andyblarblar/timebay/rust_ws/sensor_node/src/dist_sensor.rs

//! Abstractions over the distance sensor

use async_trait::async_trait;
use rand::RngCore;
use std::cmp::max;
use std::io;
use std::time::Duration;
use tf_luna::TfLuna;
use thiserror::Error;

/// A sensor capable of reading distance values.
#[async_trait]
pub trait DistanceSensor {
    /// Gets a distance reading.
    async fn get_reading(&mut self) -> Result<DistanceReading, SensorError>;
}

/// Errors from interacting with the sensor
#[derive(Error, Debug)]
pub enum SensorError {
    #[error(transparent)]
    IOError(#[from] io::Error),
    #[error(transparent)]
    LunaErr(#[from] tf_luna::error::Error),
}

/// A distance reading
pub struct DistanceReading {
    /// Distance reading in mm
    pub dist: u32,
}

impl DistanceReading {
    pub fn new(dist: u32) -> Self {
        Self { dist }
    }
}

/// Reads random distance values between two bounds.
pub struct MockDistanceReader {
    max: u32,
    min: u32,
}

impl MockDistanceReader {
    /// Creates a mock sensor that reads random values between min and max.
    pub fn new(min: u32, max: u32) -> Self {
        Self { max, min }
    }
}

#[async_trait]
impl DistanceSensor for MockDistanceReader {
    async fn get_reading(&mut self) -> Result<DistanceReading, SensorError> {
        tokio::time::sleep(Duration::from_millis(30)).await;
        Ok(DistanceReading::new(max(
            self.min,
            rand::thread_rng().next_u32() % self.max,
        )))
    }
}

#[async_trait]
impl DistanceSensor for TfLuna {
    async fn get_reading(&mut self) -> Result<DistanceReading, SensorError> {
        Ok(self
            .read()
            .await
            .map(|x| DistanceReading::new(x.dist as u32 * 10))?)
    }
}
