andyblarblar/timebay/rust_ws/sensor_node/src/application.rs

//! Sensor node application logic

use crate::dist_sensor::{DistanceReading, DistanceSensor, SensorError};
use std::time::Instant;

/// Sensor node specific application state
pub struct ApplicationContext<T>
where
    T: DistanceSensor,
{
    sensor: T,
    /// Current sensor zero, mm
    zero: u32,
    /// Delta off of zero to count as a trigger, mm
    threshold: u32,
    /// Last time we detected a car (Monotonic). Used to prevent the sensor from triggering over
    /// and over again if the vehicle is slowly passing.
    last_detection: Instant,
}

impl<T: DistanceSensor> ApplicationContext<T> {
    /// Creates a new context. Sensor should already be connected and ready.
    ///
    /// # Args
    /// `threshold` - The difference off zero to consider a trigger in mm
    pub fn new(sensor: T, default_zero: u32, threshold: u32) -> Self {
        Self {
            sensor,
            zero: default_zero,
            threshold,
            last_detection: Instant::now(),
        }
    }

    /// Zeros the sensor. New zero is stored internally, and also returned.
    pub async fn zero(&mut self) -> Result<u32, SensorError> {
        let mut avg = 0;

        for _ in 1..=100 {
            avg += self.sensor.get_reading().await?.dist;
        }

        let zero = avg / 100;
        self.zero = zero;

        log::debug!("Set zero to {}mm", zero);

        Ok(zero)
    }

    /// Spins until the sensor gets a reading that it considers to be a vehicle passing.
    pub async fn wait_for_trigger(&mut self) -> Result<DistanceReading, SensorError> {
        loop {
            let reading = self.sensor.get_reading().await?;

            if should_trigger(self.zero, self.threshold, reading.dist) {
                /* Prevent the sensor from triggering on a slow passing car over and over again by enforcing
                that each successful trigger must be followed by a 2s period of no triggers before triggering again */
                let time_since_last_detection = Instant::now().duration_since(self.last_detection);
                self.last_detection = Instant::now();
                if time_since_last_detection.as_millis() < 2000 {
                    log::trace!("Rejecting trigger due to debounce");
                    continue;
                }

                log::info!("Triggered!");

                return Ok(reading);
            }
        }
    }
}

/// Checks if a reading counts as a trigger of the car passing
fn should_trigger(zero: u32, threshold: u32, reading: u32) -> bool {
    let closer_than_zero = (zero as i64 - reading as i64) > 0;
    closer_than_zero && (zero - reading) >= threshold
}

#[cfg(test)]
mod test {
    use crate::application::should_trigger;

    #[test]
    fn should_trigger_works() {
        // Reading greater than zero should not trigger
        assert!(!should_trigger(8, 1, 9));

        // Reading exactly the trigger should trigger
        assert!(should_trigger(8, 1, 7));

        // Reading less than trigger should trigger
        assert!(should_trigger(8, 1, 1));
    }
}
