andyblarblar/timebay/rust_ws/timebay_tui/src/mqttsub.rs

//! MQTT subs as a futures stream

use crate::app::{AppMessage, AppState};
use crate::mqtt::MqttClient;
use futures::Stream;
use std::sync::Arc;
use timebay_common::error::MqttClientError;
use timebay_common::messages::MqttMessage;

type SharedMqtt = Arc<MqttClient>;

/// MQTT connection state machine
enum State {
    /// Initial connection
    Connecting(String),
    /// Spinning over connections
    Connected(SharedMqtt),
    /// Attempting to reconnect after first connection
    Reconnecting(SharedMqtt),
}

/// Infinite stream of MQTT messages. This function will manage connecting and reconnecting to the
/// broker internally.
pub fn mqtt_subscription(broker_host: String) -> impl Stream<Item = AppMessage> {
    // This is a state machine that advances between gui updates. It handles the passive communication with mqtt
    futures::stream::unfold(State::Connecting(broker_host), |state| async move {
        match state {
            State::Connecting(host) => {
                // Loop until we connect to broker
                let cli = loop {
                    let cli = MqttClient::connect(&format!("mqtt://{}:1883", &host)).await;

                    if let Err(err) = cli {
                        log::error!("Failed to connect to server with: {}", err);
                        continue;
                    }

                    break cli.unwrap();
                };

                let cli = Arc::new(cli);

                log::info!("Connected to broker!");
                Some((
                    AppMessage::StateChange(AppState::Connected { cli: cli.clone() }),
                    State::Connected(cli),
                ))
            }
            State::Connected(client) => {
                // Attempt to receive detection
                let res = client.recv_mqtt_msg().await;

                match res {
                    Ok(msg) => match msg {
                        MqttMessage::Connection(msg) => {
                            Some((AppMessage::ConnectNode(msg), State::Connected(client)))
                        }
                        MqttMessage::Disconnection(msg) => {
                            Some((AppMessage::DisconnectNode(msg), State::Connected(client)))
                        }
                        MqttMessage::Detection(msg) => {
                            Some((AppMessage::Detection(msg), State::Connected(client)))
                        }
                        _ => Some((AppMessage::Nop, State::Connected(client))),
                    },
                    Err(err) => match err {
                        MqttClientError::ConnectionErr(_) | MqttClientError::ExplicitDisconnect => {
                            log::error!("Broker disconnected!");
                            // Transition gui state to disconnect
                            Some((
                                AppMessage::StateChange(AppState::Connecting),
                                State::Reconnecting(client),
                            ))
                        }
                        MqttClientError::SerializationErr(_) => {
                            log::error!("Serialization failed!");
                            Some((AppMessage::Nop, State::Connected(client)))
                        }
                    },
                }
            }
            State::Reconnecting(client) => {
                log::info!("Attempting reconnect...");

                match client.reconnect().await {
                    Ok(_) => {
                        log::info!("Reconnected to broker!");
                        Some(
                            // Transition gui back to connected
                            (
                                AppMessage::StateChange(AppState::Connected {
                                    cli: client.clone(),
                                }),
                                State::Connected(client),
                            ),
                        )
                    }
                    Err(err) => {
                        log::error!("Erred with: {} when attempting reconnect!", err);
                        Some((AppMessage::Nop, State::Reconnecting(client)))
                    }
                }
            }
        }
    })
}
